adwjli/bluetooth-tracker/raster/bluetooth-tracker-Front-bare.png

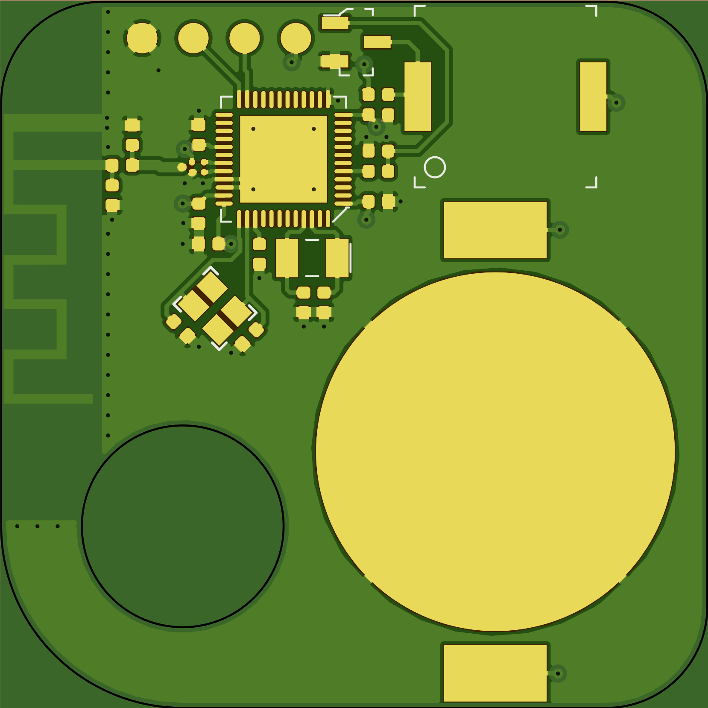
raster/bluetooth-tracker-Front-bare.png
